huisenlim/EGL314TeamD/Final/images/Q1.jpg

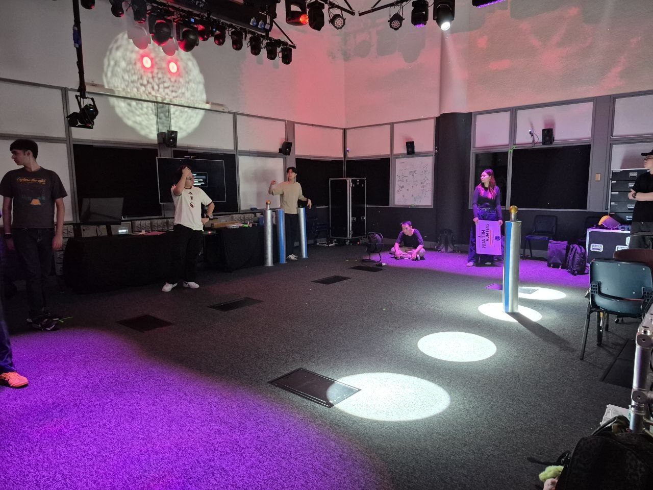
Final/images/Q1.jpg
