huisenlim/EGL314TeamD/Final/images/Q2.jpg

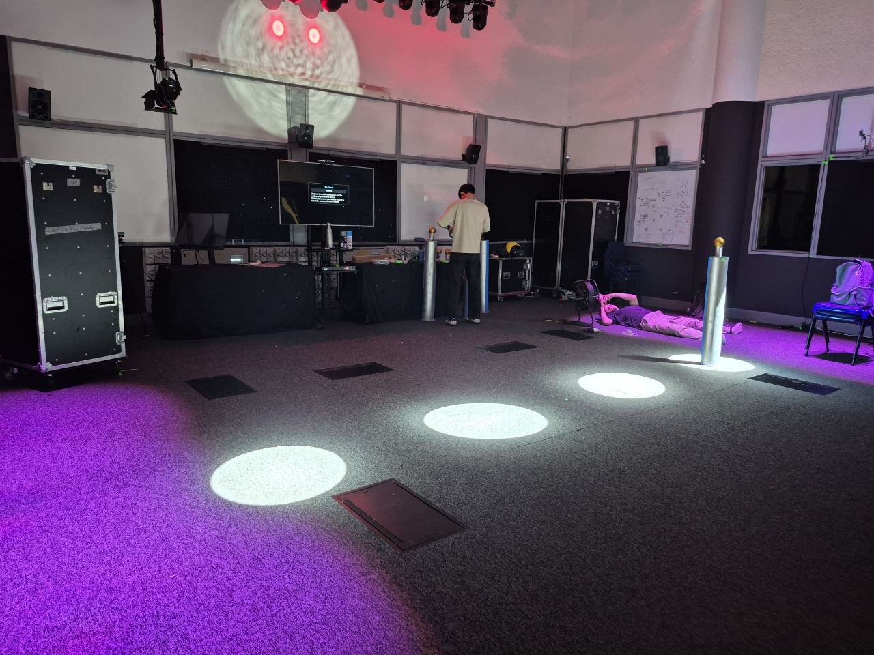
Final/images/Q2.jpg
