huisenlim/EGL314TeamD/images/multiplayOSC.png

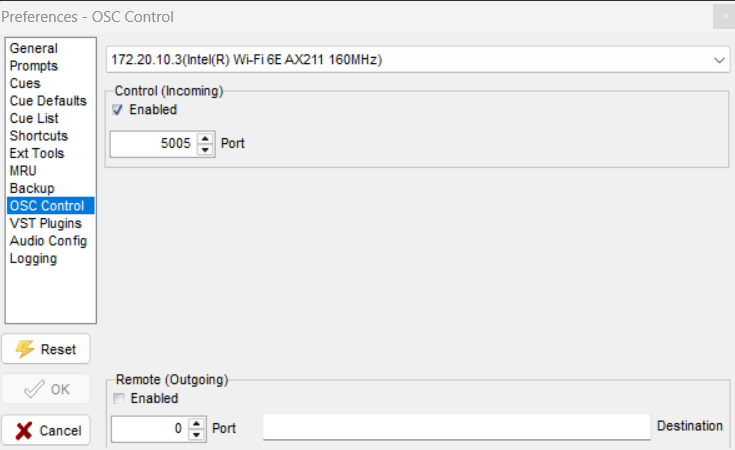
images/multiplayOSC.png
