huisenlim/EGL314TeamD/images/MultiplayPref.png

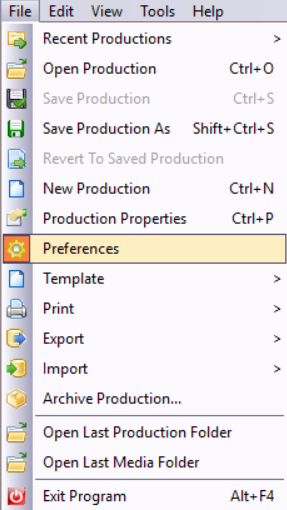
images/MultiplayPref.png
